andreasbastian-xx/3dp/autoCAD models/1x40x0.5_bar.stl

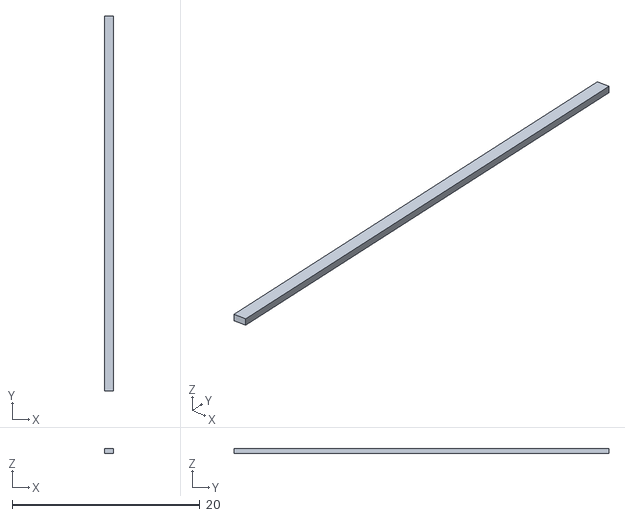
[picture p15: CAD file, 2011-07-31]
autoCAD models/1x40x0.5_bar.stl
1.00 x 40.0 x 0.5
