andreasbastian-xx/3dp/test_files/1mmSquare.stl

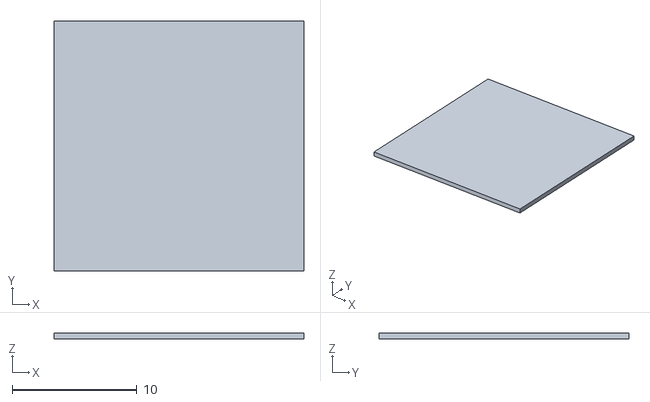
[picture p16: CAD file, 2011-07-29]
test_files/1mmSquare.stl
20.0 x 20.0 x 0.5
